timkostka/cert3d/firmware/GSL/inc/gsl_tim_defines.h

#pragma once

#include "gsl_includes.h"

// pins structure
struct GSL_TIM_PinsStruct {
  // CH1
  PinEnum ch1;
  // CH2
  PinEnum ch2;
  // CH3
  PinEnum ch3;
  // CH4
  PinEnum ch4;
  // ETR
  PinEnum etr;
  // CH1N
  PinEnum ch1n;
  // CH2N
  PinEnum ch2n;
  // CH3N
  PinEnum ch3n;
};

// timer trigger mapping
struct GSL_TIM_TriggerStruct {
  TIM_TypeDef * target;
  TIM_TypeDef * source;
  uint32_t trigger;
};

// hold trigger mappings between timers
const GSL_TIM_TriggerStruct gsl_tim_trigger[] = {
    {TIM1, TIM5, TIM_TS_ITR0},
    {TIM1, TIM2, TIM_TS_ITR1},
    {TIM1, TIM3, TIM_TS_ITR2},
    {TIM1, TIM4, TIM_TS_ITR3},

    {TIM8, TIM1, TIM_TS_ITR0},
    {TIM8, TIM2, TIM_TS_ITR1},
    {TIM8, TIM4, TIM_TS_ITR2},
    {TIM8, TIM5, TIM_TS_ITR3},

    {TIM2, TIM1, TIM_TS_ITR0},
    {TIM2, TIM8, TIM_TS_ITR1},
    {TIM2, TIM3, TIM_TS_ITR2},
    {TIM2, TIM4, TIM_TS_ITR3},

    {TIM3, TIM1, TIM_TS_ITR0},
    {TIM3, TIM2, TIM_TS_ITR1},
    {TIM3, TIM5, TIM_TS_ITR2},
    {TIM3, TIM4, TIM_TS_ITR3},

    {TIM4, TIM1, TIM_TS_ITR0},
    {TIM4, TIM2, TIM_TS_ITR1},
    {TIM4, TIM3, TIM_TS_ITR2},
    {TIM4, TIM8, TIM_TS_ITR3},

    {TIM5, TIM2, TIM_TS_ITR0},
    {TIM5, TIM3, TIM_TS_ITR1},
    {TIM5, TIM4, TIM_TS_ITR2},
    {TIM5, TIM8, TIM_TS_ITR3},

    {TIM9, TIM2, TIM_TS_ITR0},
    {TIM9, TIM3, TIM_TS_ITR1},

    {TIM12, TIM4, TIM_TS_ITR0},
    {TIM12, TIM5, TIM_TS_ITR1},
};

// number of triggers
const uint16_t gsl_tim_trigger_count =
    sizeof(gsl_tim_trigger) / sizeof(*gsl_tim_trigger);

// ************
// *** TIM1 ***
// ************

// TIM1_CH1 pin
#ifndef GSL_TIM1_PIN_CH1
#define GSL_TIM1_PIN_CH1 kPinA8
#endif

// TIM1_CH2 pin
#ifndef GSL_TIM1_PIN_CH2
#define GSL_TIM1_PIN_CH2 kPinA9
#endif

// TIM1_CH3 pin
#ifndef GSL_TIM1_PIN_CH3
#define GSL_TIM1_PIN_CH3 kPinA10
#endif

// TIM1_CH4 pin
#ifndef GSL_TIM1_PIN_CH4
#define GSL_TIM1_PIN_CH4 kPinA11
#endif

// TIM1_ETR pin
#ifndef GSL_TIM1_PIN_ETR
#define GSL_TIM1_PIN_ETR kPinA12
#endif

// TIM1_CH1N pin
#ifndef GSL_TIM1_PIN_CH1N
#define GSL_TIM1_PIN_CH1N kPinA7
#endif

// TIM1_CH2N pin
#ifndef GSL_TIM1_PIN_CH2N
#define GSL_TIM1_PIN_CH2N kPinB0
#endif

// TIM1_CH3N pin
#ifndef GSL_TIM1_PIN_CH3N
#define GSL_TIM1_PIN_CH3N kPinB1
#endif

// pins
GSL_TIM_PinsStruct gsl_tim1_pins = {
    GSL_TIM1_PIN_CH1,
    GSL_TIM1_PIN_CH2,
    GSL_TIM1_PIN_CH3,
    GSL_TIM1_PIN_CH4,
    GSL_TIM1_PIN_ETR,
    GSL_TIM1_PIN_CH1N,
    GSL_TIM1_PIN_CH2N,
    GSL_TIM1_PIN_CH3N};

// structure for handling TIM1 functions
TIM_HandleTypeDef gsl_tim1_htim = {
    TIM1,
    {
        0xFFFF, // Prescaler
        TIM_COUNTERMODE_UP, // CounterMode
        0xFFFF, // Period
        TIM_CLOCKDIVISION_DIV1, // ClockDivision
        0x00, // RepetitionCounter
    },
    HAL_TIM_ACTIVE_CHANNEL_CLEARED,
    {nullptr, nullptr, nullptr, nullptr, nullptr, nullptr, nullptr},
    HAL_UNLOCKED,
    HAL_TIM_STATE_RESET};

// ************
// *** TIM2 ***
// ************

// TIM2_CH1 pin
#ifndef GSL_TIM2_PIN_CH1
#define GSL_TIM2_PIN_CH1 kPinA0
#endif

// TIM2_CH2 pin
#ifndef GSL_TIM2_PIN_CH2
#define GSL_TIM2_PIN_CH2 kPinA1
#endif

// TIM2_CH3 pin
#ifndef GSL_TIM2_PIN_CH3
#define GSL_TIM2_PIN_CH3 kPinA2
#endif

// TIM2_CH4 pin
#ifndef GSL_TIM2_PIN_CH4
#define GSL_TIM2_PIN_CH4 kPinA3
#endif

// TIM2_ETR pin
#ifndef GSL_TIM2_PIN_ETR
#define GSL_TIM2_PIN_ETR kPinA5
#endif

// pins
GSL_TIM_PinsStruct gsl_tim2_pins = {
    GSL_TIM2_PIN_CH1,
    GSL_TIM2_PIN_CH2,
    GSL_TIM2_PIN_CH3,
    GSL_TIM2_PIN_CH4,
    GSL_TIM2_PIN_ETR,
    kPinInvalid,
    kPinInvalid,
    kPinInvalid};

// structure for handling TIM2 functions
TIM_HandleTypeDef gsl_tim2_htim = {
    TIM2,
    {
        0xFFFF, // Prescaler
        TIM_COUNTERMODE_UP, // CounterMode
        0xFFFF, // Period
        TIM_CLOCKDIVISION_DIV1, // ClockDivision
        0x00, // RepetitionCounter
    },
    HAL_TIM_ACTIVE_CHANNEL_CLEARED,
    {nullptr, nullptr, nullptr, nullptr, nullptr, nullptr, nullptr},
    HAL_UNLOCKED,
    HAL_TIM_STATE_RESET};

// ************
// *** TIM3 ***
// ************

// TIM3_CH1 pin
#ifndef GSL_TIM3_PIN_CH1
#define GSL_TIM3_PIN_CH1 kPinA6
#endif

// TIM3_CH2 pin
#ifndef GSL_TIM3_PIN_CH2
#define GSL_TIM3_PIN_CH2 kPinA7
#endif

// TIM3_CH3 pin
#ifndef GSL_TIM3_PIN_CH3
#define GSL_TIM3_PIN_CH3 kPinB0
#endif

// TIM3_CH4 pin
#ifndef GSL_TIM3_PIN_CH4
#define GSL_TIM3_PIN_CH4 kPinB1
#endif

// TIM3_ETR pin
#ifndef GSL_TIM3_PIN_ETR
#define GSL_TIM3_PIN_ETR kPinD2
#endif

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

#ifdef TIM7

// TIM7_CH1 pin
#define GSL_TIM7_PIN_CH1 kPinInvalid

// TIM7_CH2 pin
#define GSL_TIM7_PIN_CH2 kPinInvalid

// TIM7_CH3 pin
#define GSL_TIM7_PIN_CH3 kPinInvalid

// TIM7_CH4 pin
#define GSL_TIM7_PIN_CH4 kPinInvalid

// TIM7_ETR pin
#define GSL_TIM7_PIN_ETR kPinInvalid

// pins
GSL_TIM_PinsStruct gsl_tim7_pins = {
    GSL_TIM7_PIN_CH1,
    GSL_TIM7_PIN_CH2,
    GSL_TIM7_PIN_CH3,
    GSL_TIM7_PIN_CH4,
    GSL_TIM7_PIN_ETR,
    kPinInvalid,
    kPinInvalid,
    kPinInvalid};

// structure for handling TIM7 functions
TIM_HandleTypeDef gsl_tim7_htim = {
    TIM7,
    {
        0xFFFF, // Prescaler
        TIM_COUNTERMODE_UP, // CounterMode
        0xFFFF, // Period
        TIM_CLOCKDIVISION_DIV1, // ClockDivision
        0x00, // RepetitionCounter
    },
    HAL_TIM_ACTIVE_CHANNEL_CLEARED,
    {nullptr, nullptr, nullptr, nullptr, nullptr, nullptr, nullptr},
    HAL_UNLOCKED,
    HAL_TIM_STATE_RESET};

#endif

// ************
// *** TIM8 ***
// ************

#ifdef TIM8

// TIM8_CH1 pin
#ifndef GSL_TIM8_PIN_CH1
#define GSL_TIM8_PIN_CH1 kPinC6
#endif

// TIM8_CH2 pin
#ifndef GSL_TIM8_PIN_CH2
#define GSL_TIM8_PIN_CH2 kPinC7
#endif

// TIM8_CH3 pin
#ifndef GSL_TIM8_PIN_CH3
#define GSL_TIM8_PIN_CH3 kPinC8
#endif

// TIM8_CH4 pin
#ifndef GSL_TIM8_PIN_CH4
#define GSL_TIM8_PIN_CH4 kPinC9
#endif

// TIM8_ETR pin
#ifndef GSL_TIM8_PIN_ETR
#define GSL_TIM8_PIN_ETR kPinA0
#endif

// TIM8_CH1N pin
#ifndef GSL_TIM8_PIN_CH1N
#define GSL_TIM8_PIN_CH1N kPinA5
#endif

// TIM8_CH2N pin
#ifndef GSL_TIM8_PIN_CH2N
#define GSL_TIM8_PIN_CH2N kPinB14
#endif

// TIM8_CH3N pin
#ifndef GSL_TIM8_PIN_CH3N
#define GSL_TIM8_PIN_CH3N kPinB15
#endif

// pins
GSL_TIM_PinsStruct gsl_tim8_pins = {
    GSL_TIM8_PIN_CH1,
    GSL_TIM8_PIN_CH2,
    GSL_TIM8_PIN_CH3,
    GSL_TIM8_PIN_CH4,
    GSL_TIM8_PIN_ETR,
    kPinInvalid,
    kPinInvalid,
    kPinInvalid};

// structure for handling TIM8 functions
TIM_HandleTypeDef gsl_tim8_htim = {
    TIM8,
    {
        0xFFFF, // Prescaler
        TIM_COUNTERMODE_UP, // CounterMode
        0xFFFF, // Period
        TIM_CLOCKDIVISION_DIV1, // ClockDivision
        0x00, // RepetitionCounter
    },
    HAL_TIM_ACTIVE_CHANNEL_CLEARED,
    {nullptr, nullptr, nullptr, nullptr, nullptr, nullptr, nullptr},
    HAL_UNLOCKED,
    HAL_TIM_STATE_RESET};

#endif

// ************
// *** TIM9 ***
// ************

#ifdef TIM9

// TIM9_CH1 pin
#ifndef GSL_TIM9_PIN_CH1
#define GSL_TIM9_PIN_CH1 kPinA2
#endif

// TIM9_CH2 pin
#ifndef GSL_TIM9_PIN_CH2
#define GSL_TIM9_PIN_CH2 kPinA3
#endif

// TIM9_CH3 pin
#define GSL_TIM9_PIN_CH3 kPinInvalid

// TIM9_CH4 pin
#define GSL_TIM9_PIN_CH4 kPinInvalid

// TIM9_ETR pin
#define GSL_TIM9_PIN_ETR kPinInvalid

// pins
GSL_TIM_PinsStruct gsl_tim9_pins = {
    GSL_TIM9_PIN_CH1,
    GSL_TIM9_PIN_CH2,
    GSL_TIM9_PIN_CH3,
    GSL_TIM9_PIN_CH4,
    GSL_TIM9_PIN_ETR,
    kPinInvalid,
    kPinInvalid,
    kPinInvalid};

// structure for handling TIM9 functions
TIM_HandleTypeDef gsl_tim9_htim = {
    TIM9,
    {
        0xFFFF, // Prescaler
        TIM_COUNTERMODE_UP, // CounterMode
        0xFFFF, // Period
        TIM_CLOCKDIVISION_DIV1, // ClockDivision
        0x00, // RepetitionCounter
    },
    HAL_TIM_ACTIVE_CHANNEL_CLEARED,
    {nullptr, nullptr, nullptr, nullptr, nullptr, nullptr, nullptr},
    HAL_UNLOCKED,
    HAL_TIM_STATE_RESET};

#endif

// *************
// *** TIM10 ***
// *************

#ifdef TIM10

// TIM10_CH1 pin
#ifndef GSL_TIM10_PIN_CH1
#define GSL_TIM10_PIN_CH1 kPinB8
#endif

// TIM10_CH2 pin
#define GSL_TIM10_PIN_CH2 kPinInvalid

// TIM10_CH3 pin
#define GSL_TIM10_PIN_CH3 kPinInvalid

// TIM10_CH4 pin
#define GSL_TIM10_PIN_CH4 kPinInvalid

// TIM10_ETR pin
#define GSL_TIM10_PIN_ETR kPinInvalid

// pins
GSL_TIM_PinsStruct gsl_tim10_pins = {
    GSL_TIM10_PIN_CH1,
    GSL_TIM10_PIN_CH2,
    GSL_TIM10_PIN_CH3,
    GSL_TIM10_PIN_CH4,
    GSL_TIM10_PIN_ETR,
    kPinInvalid,
    kPinInvalid,
    kPinInvalid};

// structure for handling TIM10 functions
TIM_HandleTypeDef gsl_tim10_htim = {
    TIM10,
    {
        0xFFFF, // Prescaler
        TIM_COUNTERMODE_UP, // CounterMode
        0xFFFF, // Period
        TIM_CLOCKDIVISION_DIV1, // ClockDivision
        0x00, // RepetitionCounter
    },
    HAL_TIM_ACTIVE_CHANNEL_CLEARED,
    {nullptr, nullptr, nullptr, nullptr, nullptr, nullptr, nullptr},
    HAL_UNLOCKED,
    HAL_TIM_STATE_RESET};

#endif

// *************
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
        RCC_APB2ENR_TIM9EN,
    },
#endif // #ifdef TIM9

#ifdef TIM10
    {
        TIM10,
        &gsl_tim10_htim,
        &gsl_tim10_pins,
        TIM1_UP_TIM10_IRQn,
        nullptr,
        false,
        &RCC->APB2ENR,
        RCC_APB2ENR_TIM10EN,
    },
#endif // #ifdef TIM10

#ifdef TIM11
    {
        TIM11,
        &gsl_tim11_htim,
        &gsl_tim11_pins,
        TIM1_TRG_COM_TIM11_IRQn,
        nullptr,
        false,
        &RCC->APB2ENR,
        RCC_APB2ENR_TIM11EN,
    },
#endif // #ifdef TIM11

#ifdef TIM12
    {
        TIM12,
        &gsl_tim12_htim,
        &gsl_tim12_pins,
        TIM8_BRK_TIM12_IRQn,
        nullptr,
        false,
        &RCC->APB1ENR,
        RCC_APB1ENR_TIM12EN,
    },
#endif // #ifdef TIM12

#ifdef TIM13
    {
        TIM13,
        &gsl_tim13_htim,
        &gsl_tim13_pins,
        TIM8_UP_TIM13_IRQn,
        nullptr,
        false,
        &RCC->APB1ENR,
        RCC_APB1ENR_TIM13EN,
    },
#endif // #ifdef TIM3

#ifdef TIM14
    {
        TIM14,
        &gsl_tim14_htim,
        &gsl_tim14_pins,
        TIM8_TRG_COM_TIM14_IRQn,
        nullptr,
        false,
        &RCC->APB1ENR,
        RCC_APB1ENR_TIM14EN,
    },
#endif // #ifdef TIM14

};

// number of TIM peripherals
const uint32_t GSL_TIM_PeripheralCount =
    sizeof(GSL_TIM_Info) / sizeof(*GSL_TIM_Info);

// bytes of RAM used to store all the handler structs
const uint32_t GSL_TIM_StorageByteCount =
    sizeof(GSL_TIM_Info) +
    GSL_TIM_PeripheralCount * sizeof(TIM_HandleTypeDef) +
    GSL_TIM_PeripheralCount * sizeof(GSL_TIM_PinsStruct);

// timer to use for path processing callback
//TIM_TypeDef * const qb_process_timer = TIM2;
