timkostka/cert3d/ScopePanel.py

"""
This implements a custom wx control to view .

"""

import time
import math
import wx

from dpi import asize

from Data import *

# maximum edges per screen
max_points_per_screen = 1000

# screen size in pixels
screen_size = 1000

# possible colors for signals
all_signal_colors = [
    ("Red", wx.RED),
    ("Orange", wx.Colour(255, 127, 0)),
    ("Yellow", wx.YELLOW),
    ("Green", wx.GREEN),
    ("Cyan", wx.CYAN),
    ("Blue", wx.BLUE),
    ("Magenta", wx.Colour(255, 0, 255)),
    ("White", wx.WHITE),
]


class Signal:
    """A Signal holds information about a scope signal."""

    def __init__(self, name=None, color=wx.GREEN, thickness=1, data=None):
        # raw data
        assert isinstance(data, Data)
        # name of the signal
        self.name = name
        # color of channel
        self.color = color
        # width of the channel plot in pixels
        self.thickness = thickness
        # active data set
        self.active_data = data
        # start time of the data
        self.start_time = data.start_time
        # data cluster
        self.data_cluster = [[0, data]]

    def create_simplified_data_sets(self):
        """Create simplified data sets."""
        # create simplified data sets
        if len(self.data_cluster) > 1:
            del self.data_cluster[1:]
        data = self.get_master_data()
        while data.get_point_count() > max_points_per_screen:
            new_data = data.get_reduced_data()
            if new_data is None:
                break
            self.data_cluster.append([0, new_data])
            data = new_data
        # find zoom levels for each set
        for i in range(len(self.data_cluster)):
            data = self.data_cluster[i][1]
            min_seconds = data.get_min_period_with_point_count(
                max_points_per_screen
            )
            min_pixels_per_second = screen_size / min_seconds
            self.data_cluster[i][0] = min_pixels_per_second
        # DEBUG
        if False:
            print([(x[1].get_point_count(), x[0]) for x in self.data_cluster])
        # set min zoom level of most simplified set to 0
        self.data_cluster[-1][0] = 0.0

    def get_master_data(self):
        return self.data_cluster[0][1]

    def is_empty(self):
        """Return True if the signal is empty."""
        return bool(self.data_cluster)

    def set_active_data(self, pixels_per_second):
        """Set the active data based on the pixels_per_second value."""
        raise NotImplementedError

    def get_start_time(self):
        """Return the start time of the signal data in seconds."""
        if not self.active_data or self.active_data.is_empty():
            return 0.0
        return self.active_data.get_time_at_index(0)

    def get_length(self):
        """Return the length of the signal data in seconds."""
        if not self.active_data:
            return 0.0
        return self.active_data.get_length()

    def draw_signal(self, *args, **kwargs):
        """Draw the signal"""
        if not self.active_data:
            return
        self.active_data.draw_signal(*args, **kwargs)


class ScopeChannel:
    def __init__(self, height=30, low_value=0.0, high_value=1.0, signal=None):
        # height of channel in pixels
        self.height = height
        # value at low end of channel
        # (not used for bilevel or tristate signals)
        self.low_value = None
        # value at high end of channel
        # (not used for bilevel or tristate signals)
        self.high_value = None
        # signals within this scope channel
        self.signals = []
        # add data if needed
        if signal:
            self.add_signal(signal)

    def add_signal(self, signal):
        self.signals.append(signal)

    def draw(self, dc):
        """Draw the channel clipped to the given rectangle DC."""
        raise NotImplementedError


class ScopePanel(wx.ScrolledWindow):
    """A ScopePanel is a custom wxWidget to display oscilloscope-type data."""

    def __init__(self, parent, id_, position, size, style):
        super().__init__(parent, id_, position, size, style)
        # get estimated number of pixels per screen
        global screen_size
        screen_size = asize(1920)
        # create popup menu for signal style
        self.style_popup_menu = self.create_style_menu()
        self.SetBackgroundStyle(wx.BG_STYLE_PAINT)
        # list of channels
        self.channels = []
        # maximum zoom level to 10 pixels per ns
        self.maximum_pixels_per_second = asize(5) / 1e-9
        # minimum zoom level
        self.minimum_pixels_per_second = 0.0
        # index of selected channel, or None
        self.selected_channel_index = None
        # link to vertical scroll bar
        self.vertical_scroll_bar = None
        # (channel_index, y_value) used during rearranging channels
        self.dragging_channel = None
        # width of the snaptime display
        self.snaptime_frame_thickness = asize(1)
        # color of snaptime display
        self.snaptime_frame_color = wx.YELLOW
        # color of snaptime text
        self.snaptime_text_color = wx.WHITE
        # padding between name and channel data
        self.padding2 = asize(2)
        # thickness in pixels of channel separator bar
        self.channel_separator_thickness = 1
        # padding between channels
        self.padding = 2 * asize(2) + self.channel_separator_thickness
        # margin in pixels all around
        self.margin = asize(2)
        # spacing between signals
        self.signal_spacing = asize(2)
        # padding around timestamp label
        self.padding_timestamp_label = asize(1)
        # length of channel
        self.channel_length = asize(120)
        # leftmost time
        self.start_time = 0.0
        # zoom factor in pixels per second
        self.pixels_per_second = 1.0
        # mouse panning memory
        self.panning = False
        self.panning_start = 0
        # holds the (channel_index, signal_index) for a style menu popup
        self.signal_to_style = None
        # true when we're selecting a time delta
        self.selecting_time = False
        # maximum distance in pixels to snap to a time value
        self.snap_distance = asize(10)
        # offset in y pixels
        self.y_offset = 0
        # desired height to fit all channels in pixels
        self.desired_height = 0
        # minimum time of all data
        self.minimum_time = 0.0
        # maximum time of all data
        self.maximum_time = 0.0
        # delta time unit for horizontal axis (e.g. 10e-9)
        self.best_dt = None
        # highlighted point
        # (time, y_pixel)
        self.highlighted_point = None
        # name of the dt (e.g. "10 ns")
        self.best_dt_text = None
        # font for signal lables
        self.font_signal_name = wx.Font(
            9,
            wx.FONTFAMILY_MODERN,
            wx.FONTSTYLE_NORMAL,
            wx.FONTWEIGHT_BOLD,
            False,
            "Consolas",
        )
        # get height of signal names in pixels
        dc = wx.ClientDC(self)
        dc.SetFont(self.font_signal_name)
        # height of a signal name in pixels
        self.signal_name_height = dc.GetFullTextExtent("X")[1]
        # print("Signal name height is", self.signal_name_height)
        # font for timestamps
        self.font_timestamp = wx.Font(
            9,
            wx.FONTFAMILY_MODERN,
            wx.FONTSTYLE_NORMAL,
            wx.FONTWEIGHT_BOLD,
            False,
            "Calibri",
        )
        # margin for snaptime label
        self.snaptime_margin = [1, 0]
        # either None or (channel_index, signal_index, time)
        self.snaptime_start = None
        self.snaptime_end = None
        # prevent panel from shrinking too much
        self.SetMinSize((200, 200))
        # store stipple brushes
        self.stipple_brushes = {}
        # set background
        self.SetBackgroundColour(wx.BLACK)
        self.SetForegroundColour(wx.WHITE)

        self.Bind(wx.EVT_MENU, self.event_popup_menu_item_selected)
        self.Bind(wx.EVT_CONTEXT_MENU, self.event_show_popup)
        self.Bind(wx.EVT_PAINT, self.event_paint)
        self.Bind(wx.EVT_LEFT_DOWN, self.event_mouse_left_button_down)
        self.Bind(wx.EVT_LEFT_UP, self.event_mouse_left_button_up)
        self.Bind(wx.EVT_MIDDLE_DOWN, self.event_mouse_middle_button_down)
        self.Bind(wx.EVT_MIDDLE_UP, self.event_mouse_middle_button_up)
        self.Bind(wx.EVT_MOTION, self.event_mouse_motion)
        self.Bind(wx.EVT_LEAVE_WINDOW, self.event_leave_window)
        self.Bind(wx.EVT_MOUSEWHEEL, self.event_mouse_wheel)
        self.Bind(wx.EVT_SIZE, self.event_on_size)

        self.adjust_channel_name_size()

        # DEBUG populate sample data
        self.populate_example_data()

        self.zoom_to_all()

    def redo_scroll_bars(self):
        """Show/hide scroll bars based on current state."""
        self.SetScrollbars(1, 1, 1, self.desired_height)
        return
        # if no data, hide scroll bars
        width, height = self.GetSize()
        if not self.channels:
            show_vertical_bar = False
            show_horizontal_bar = False
        else:
            # get y position of last channel
            show_vertical_bar = height < self.desired_height
        # see if we need to show or hide the vertical bar
        vertical_bar_shown = self.GetParent().scroll_bar_vertical.IsShown()
        # show or hide bar
        if vertical_bar_shown != show_vertical_bar:
            self.GetParent().scroll_bar_vertical.Show(show_vertical_bar)
        # if vertical bar is hidden, we have no offset
        if not show_vertical_bar:
            self.y_offset = 0
        # update ticks
        if show_vertical_bar:
            self.GetParent().scroll_bar_vertical.SetScrollbar(
                self.y_offset, height, self.desired_height, asize(10)
            )
        return
        horizontal_bar_shown = self.GetParent().show_horizontal_bar.IsShown()
        # find x pixel of leftmost time
        x_low = self.get_x_from_time(self.minimum_time)
        x_high = self.get_x_from_time(self.maximum_time)
        # get first x pixel
        first_x = self.margin + self.channel_length + self.padding2
        # TODO: implement this
        show_horizontal_bar = x_low < first_x

        # either show or hide horizontal bar
        if horizontal_bar_shown != show_horizontal_bar:
            self.GetParent().scroll_bar_horizontal.Show(show_horizontal_bar)
        # update horizontal bar
        wanted_width = 0

    def event_on_size(self, _event):
        self.redo_scroll_bars()

    def clear(self):
        """Erase all channels."""
        self.channels = []

    def populate_example_data(self):
        """Populate the display with fabricated."""
        self.clear()
        # add some junk data
        for name in [
            "X_STEP",
            "X_DIR",
            "Y_STEP",
            "Y_DIR",
            "Z_STEP",
            "Z_DIR",
            "E_STEP",
            "E_DIR",
        ]:
            # create a random signal
            if "DIR" in name and False:
                data = TriStateData()
            else:
                data = BilevelData()
            data.invent_data(2000)
            signal = Signal(name=name, color=wx.GREEN, thickness=1, data=data)
            signal.create_simplified_data_sets()
            # create a channel for this signal
            channel = ScopeChannel(height=40, signal=signal)
            # add this channel
            self.add_channel(channel)
        for i in range(3):
            name = 'FuzzyData%d' % i
            data = FuzzyPlotData()
            signal = Signal(name=name, color=wx.GREEN, thickness=1, data=data)
            channel = ScopeChannel(height=120, signal=signal)
            self.add_channel(channel)
        for name in ["X_POS", "Y_POS", "Z_POS", "E_POS"]:
            data = PlotData()
            data.invent_data(5000)
            signal = Signal(name=name, color=wx.CYAN, thickness=1, data=data)
            signal.create_simplified_data_sets()
            channel = ScopeChannel(height=120, signal=signal)
            self.add_channel(channel)

    def adjust_channel_name_size(self):
        """Find ideal value for self.channel_length."""
        max_length = 0
        dc = wx.ClientDC(self)
        dc.SetFont(self.font_signal_name)
        for channel in self.channels:
            for signal in channel.signals:
                rect = dc.GetFullTextExtent(signal.name)
                max_length = max(max_length, rect[0])
        if max_length > 0:
            self.channel_length = max_length + asize(5)

    def create_style_menu(self):
        """Create and return a wx.Menu for the signal style popup."""
        menu = wx.Menu()
        # add colors
        # item = menu.Append(-1, "Color")
        submenu = wx.Menu()
        for (name, color) in all_signal_colors:
            submenu.AppendRadioItem(-1, name)
        menu.AppendSubMenu(submenu, "&Color")
        # add thickness submenu
        submenu = wx.Menu()
        for i in range(1, 6):
            submenu.AppendRadioItem(-1, str(i))
        menu.AppendSubMenu(submenu, "&Thickness")
        menu.Append(wx.MenuItem(menu, -1, "&Master data"))
        menu.Append(wx.MenuItem(menu, -1, "&All master data"))
        return menu

    def update_desired_height(self):
        if not self.channels:
            self.desired_height = 0
            return
        # update desired height
        self.desired_height = 2 * self.margin
        self.desired_height += (len(self.channels) - 1) * self.padding
        self.desired_height += sum(x.height for x in self.channels)

    def add_channel(self, channel):
        """Add a new channel."""
        self.channels.append(channel)
        self.update_desired_height()

    def get_channel_from_y(self, y):
        """Return the channel index for the given y pixel, or None."""
        for i in range(len(self.channels)):
            y1, y2 = self.get_channel_y_values(i)
            # return None if we've passed it already
            if y1 > y:
                return None
            if y1 <= y <= y2:
                return i
        # return None if we're past the end of the data
        return None

    def get_signal_from_y(self, y):
        """Return the channel and signal index from the y pixel, or None."""
        channel_index = self.get_channel_from_y(y)
        if channel_index is None:
            return None
        # search through signals in this channel
        signal_count = len(self.channels[channel_index].signals)
        y1, y2 = self.get_channel_y_values(channel_index)
        # get y value of middle of channel
        y_mid = (y1 + y2) // 2
        # get y value of first signal
        name_height = (
            signal_count * self.signal_name_height
            + (signal_count - 1) * self.signal_spacing
        )
        y_top = y_mid - name_height // 2
        for signal_index in range(signal_count):
            if signal_index > 0:
                y_top += self.signal_spacing + self.signal_name_height
            if y_top <= y < y_top + self.signal_name_height:
                return channel_index, signal_index
        # return None if we're past the end of the data
        return None

    def find_snaptime(self, position):
        """Return the snaptime at the given position, or None"""
        # find correct channel
        x, y = position
        channel_index = self.get_channel_from_y(y)
        if channel_index is None:
            return None
        # alias this channel
        channel = self.channels[channel_index]
        # convert pixel position to a time
        target_time = self.get_time_from_x(x)
        # hold a list of closest time for each signal within the channel
        best_delta = 0.0
        closest_time = None
        # find the closest x value for each signal within the channel
        for signal_index, signal in enumerate(channel.signals):
            this_time = signal.active_data.get_edge_near_time(target_time)
            if this_time is not None:
                this_delta = abs(this_time - target_time)
                if closest_time is None or this_delta < best_delta:
                    best_delta = this_delta
                    closest_time = (channel_index, signal_index, this_time)
        if closest_time is None:
            return None
        # find delta in pixels
        pixel_delta = int(best_delta * self.pixels_per_second + 0.5)
        if abs(pixel_delta) < self.snap_distance:
            return closest_time
        return None

    def event_mouse_left_button_down(self, event):
        # we either try to drag a channel, or try to select a snapline
        x_separator = self.margin + self.channel_length + self.padding2
        if event.GetPosition()[0] < x_separator:
            # reset snaptime if present
            y = event.GetPosition()[1]
            for i in range(len(self.channels)):
                y1, y2 = self.get_channel_y_values(i)
                if y1 <= y <= y2:
                    # print('Dragging channel', self.dragging_channel)
                    self.dragging_channel = (i, y - y1)
                    self.selected_channel_index = i
                    self.Refresh()
                    break
        else:
            # find closest
            old_start = self.snaptime_start
            old_end = self.snaptime_end
            self.snaptime_start = None
            self.snaptime_end = None
            self.snaptime_start = self.find_snaptime(event.GetPosition())
            if (
                self.snaptime_start != old_start
                or self.snaptime_end != old_end
            ):
                self.Refresh()
            self.selecting_time = bool(self.snaptime_start)

    def event_mouse_left_button_up(self, event):
        if self.dragging_channel:
            self.dragging_channel = None
            self.selected_channel_index = None
            self.Refresh()
        self.selecting_time = False
        if self.snaptime_start:
            self.snaptime_end = self.find_snaptime(event.GetPosition())
            if (
                not self.snaptime_end
                or self.snaptime_end == self.snaptime_start
            ):
                self.snaptime_start = None
                self.snaptime_end = None
            self.Refresh()

    def get_time_at_mouse(self, event):
        """Return the time at the mouse coordinates."""
        pass

    def event_leave_window(self, event):
        if self.panning:
            self.event_mouse_middle_button_up(event)
        if self.dragging_channel:
            self.event_mouse_left_button_up(event)

    def event_mouse_middle_button_down(self, event):
        # print('right button down')
        x = event.GetPosition()[0]
        if x >= self.margin + self.channel_length + self.padding2:
            self.panning_start = x
            self.panning = True
            self.SetCursor(wx.Cursor(wx.CURSOR_SIZEWE))

    def event_mouse_middle_button_up(self, _event):
        # print('right button up')
        if self.panning:
            self.SetCursor(wx.Cursor(wx.CURSOR_DEFAULT))
            self.panning = False

    def event_mouse_motion(self, event):
        if self.panning:
            dx = event.GetPosition()[0] - self.panning_start
            # if no net motion, just return
            if not dx:
                return
            # print('moved by %d pixels' % dx)
            delta = dx / self.pixels_per_second
            self.start_time -= delta
            self.panning_start += dx
            self.Refresh()
        elif self.dragging_channel:
            # get offset into current channel as-is
            index, offset = self.dragging_channel
            y1, _ = self.get_channel_y_values(index)
            this_offset = event.GetPosition()[1] - y1
            # get target amount of pixels to move channel
            current_delta = this_offset - offset
            chan = self.channels
            if current_delta > 0 and index < len(self.channels) - 1:
                # set a 2 pixel hysteresis
                current_delta -= 1
                # get delta if we move channel down
                increase = self.channels[index + 1].height + self.padding
                # see if it's advantageous to move it
                if abs(current_delta - increase) < abs(current_delta):
                    chan[index], chan[index + 1] = chan[index + 1], chan[index]
                    index += 1
                    self.dragging_channel = (index, offset)
                    self.selected_channel_index = index
                    self.Refresh()
            elif current_delta < 0 and index > 0:
                # set a 2 pixel hysteresis
                current_delta += 1
                # get delta if we move channel up
                increase = self.channels[index - 1].height + self.padding
                # see if it's advantageous to move it
                if abs(current_delta + increase) < abs(current_delta):
                    chan[index - 1], chan[index] = chan[index], chan[index - 1]
                    index -= 1
                    self.dragging_channel = (index, offset)
                    self.selected_channel_index = index
                    self.Refresh()
        elif self.snaptime_start and self.selecting_time:
            new_end = self.find_snaptime(event.GetPosition())
            if new_end != self.snaptime_end:
                self.snaptime_end = new_end
                if self.snaptime_end == self.snaptime_start:
                    self.snaptime_end = None
                self.Refresh()
        else:
            y = event.GetPosition()[1]
            channel_index = None
            for i in range(len(self.channels)):
                y1, y2 = self.get_channel_y_values(i)
                if y1 <= y <= y2:
                    # print('Dragging channel', self.dragging_channel)
                    channel_index = i
                    break
            if channel_index is None:
                return
            # find tick value
            signal = self.channels[channel_index].signals[0]
            x = event.GetPosition()[0]
            x_separator = self.margin + self.channel_length + self.padding2
            if x < x_separator:
                return
            x -= x_separator
            t = self.start_time + x / self.pixels_per_second
            i = signal.active_data.find_closest_index(t)
            if i is None:
                return
            text = "index %d, time %g" % (channel_index, t)
            if isinstance(signal.active_data, PlotData):
                y = signal.active_data.points[i][1]
                text += ", value=%g" % y
            self.GetParent().GetParent().GetParent().status_bar.SetStatusText(text)

    def event_mouse_wheel(self, event):
        """Handle scrolling in/out via the mouse wheel."""
        scale = 2.0 ** (1.0 / 3.0)
        # if Ctrl is held, zoom faster
        if wx.GetKeyState(wx.WXK_SHIFT):
            scale = 2.0
        if event.GetWheelRotation() < 0:
            scale = 1.0 / scale
        dx = self.margin + self.channel_length + self.padding2
        # get min and max scale
        max_scale = self.maximum_pixels_per_second / self.pixels_per_second
        min_scale = self.minimum_pixels_per_second / self.pixels_per_second
        assert min_scale <= max_scale
        # clip scale to min, max bounds
        scale = max(min_scale, min(scale, max_scale))
        # adjust start time so time at cursor remains the same
        x = event.GetPosition()[0]
        # apply the scale
        if scale != 1.0:
            self.pixels_per_second *= scale
            self.start_time -= (x - dx) / self.pixels_per_second * (1 - scale)
            self.update_signal_zoom()
            self.Refresh()

    def get_x_from_time(self, duration):
        """Return the x pixels corresponding to the given duration."""
        x = self.margin + self.channel_length + self.padding2
        x += (duration - self.start_time) * self.pixels_per_second
        return int(x + 0.5)

    def get_time_from_x(self, x):
        """Return the time value corresponding to the x position."""
        x -= self.margin + self.channel_length + self.padding2
        return self.start_time + x / self.pixels_per_second

    def get_channel_y_values(self, channel_index):
        """Return the top and bottom y pixels for the given channel."""
        top = self.margin - self.y_offset
        top += sum(x.height for x in self.channels[:channel_index])
        top += channel_index * self.padding
        return top, top + self.channels[channel_index].height - 1

    def update_signal_zoom(self):
        """Find the best data for the given zoom level."""
        for channel in self.channels:
            for signal in channel.signals:
                if signal.is_empty():
                    signal.active_data = None
                signal.active_data = None
                for zoom, data in signal.data_cluster:
                    if zoom < self.pixels_per_second:
                        signal.active_data = data
                        break
                assert signal.active_data is not None

    def zoom_to_all(self, include_zero=True):
        """Initialize the viewing window to see all data."""
        if not self.channels:
            return
        start_times = []
        end_times = []
        for channel in self.channels:
            for signal in channel.signals:
                start = signal.get_start_time()
                length = signal.get_length()
                start_times.append(start)
                end_times.append(start + length)
        left = min(start_times) if start_times else 0.0
        right = max(end_times) if end_times else 0.0
        panel_width = (
            self.GetSize()[0]
            - 2 * self.margin
            - self.padding2
            - self.channel_length
        )
        panel_width = max(panel_width, asize(200))
        self.start_time = left
        self.pixels_per_second = 1.0
        if right != left:
            self.pixels_per_second = (panel_width - 1) / (right - left)
        self.update_signal_zoom()
        self.Refresh()
        for channel in self.channels:
            low_values = []
            high_values = []
            for signal in channel.signals:
                data = signal.active_data
                if data.is_empty():
                    continue
                if isinstance(data, PlotData):
                    low_values.append(min(x[1] for x in data.points))
                    high_values.append(max(x[1] for x in data.points))
                elif isinstance(data, FuzzyPlotData):
                    low_values.append(min(x[1] for x in data.points))
                    high_values.append(max(x[2] for x in data.points))
            if low_values:
                channel.low_value = min(low_values)
                if include_zero:
                    channel.low_value = min(0.0, channel.low_value)
                channel.high_value = max(high_values)
                if include_zero:
                    channel.high_value = max(0.0, channel.high_value)
                if channel.low_value == channel.high_value:
                    channel.high_value = channel.low_value + 1e99

    def trim_signals(self, idle_ms=100):
        """Trim inactivity from the start and end of all signals."""
        # get first time of activity
        first_activity = []
        last_activity = []
        for channel in self.channels:
            for signal in channel.signals:
                data = signal.get_master_data()
                if isinstance(data, PlotData):
                    data.optimize()
                if data.get_point_count() < 2:
                    continue
                if isinstance(data, PlotData) or isinstance(data, FuzzyPlotData):
                    continue
                    if data.points[0][1] == data.points[1][1]:
                        first_activity.append(data.get_time_at_index(1))
                    else:
                        first_activity.append(data.get_time_at_index(0))
                    if data.points[-1][1] == data.points[-2][1]:
                        last_activity.append(data.get_time_at_index(-2))
                    else:
                        last_activity.append(data.get_time_at_index(-1))
                elif isinstance(data, BilevelData):
                    first_activity.append(data.get_time_at_index(1))
                    last_activity.append(data.get_time_at_index(-2))
                elif isinstance(data, TriStateData):
                    first_activity.append(data.get_time_at_index(1))
                    last_activity.append(data.get_time_at_index(-2))
                else:
                    raise ValueError("type %s is unexpected" % type(data))
        # find values to trim to
        if first_activity:
            start_time = min(first_activity) - idle_ms / 1000.0
        else:
            start_time = None
        if last_activity:
            end_time = max(last_activity) + idle_ms / 1000.0
        else:
            end_time = None
        if start_time > end_time:
            return
        # trim start
        if start_time:
            for channel in self.channels:
                for signal in channel.signals:
                    data = signal.get_master_data()
                    if (
                        data.is_empty()
                        or data.get_time_at_index(0) > start_time
                    ):
                        continue
                    tick = data.get_x_from_time(start_time)
                    if isinstance(data, BilevelData):
                        data.edges[0] = tick
                    else:
                        data.points[0] = (tick, data.points[0][1])
        if end_time:
            for channel in self.channels:
                for signal in channel.signals:
                    data = signal.get_master_data()
                    if (
                        data.is_empty()
                        or data.get_time_at_index(-1) < end_time
                    ):
                        continue
                    tick = data.get_x_from_time(end_time)
                    if isinstance(data, BilevelData):
                        data.edges[-1] = tick
                    else:
                        data.points[-1] = (tick, data.points[-1][1])
                    signal.create_simplified_data_sets()
        self.Refresh()

    @staticmethod
    def time_to_text(time_s):
        """Convert the time in seconds to a text value."""
        if time_s == 0:
            return "0"
        abstime = abs(time_s)
        if abstime < 10e-9:
            return "%.2f ns" % (time_s * 1e9)
        elif abstime < 100e-9:
            return "%.1f ns" % (time_s * 1e9)
        elif abstime < 1000e-9:
            return "%.0f ns" % (time_s * 1e9)
        elif abstime < 10e-6:
            return "%.2f us" % (time_s * 1e6)
        elif abstime < 100e-6:
            return "%.1f us" % (time_s * 1e6)
        elif abstime < 1000e-6:
            return "%.0f us" % (time_s * 1e6)
        elif abstime < 10e-3:
            return "%.2f ms" % (time_s * 1e3)
        elif abstime < 100e-3:
            return "%.1f ms" % (time_s * 1e3)
        elif abstime < 1000e-3:
            return "%.0f ms" % (time_s * 1e3)
        else:
            return "%g s" % time_s

    def find_dt(self):
        """Evaluate the best time delta for the given scale."""
        # get the width of some standard text
        dc = wx.PaintDC(self)
        dc.SetFont(
            wx.Font(
                9,
                wx.FONTFAMILY_MODERN,
                wx.FONTSTYLE_NORMAL,
                wx.FONTWEIGHT_NORMAL,
                False,
                "Consolas",
            )
        )
        rect = dc.GetFullTextExtent("Target width    ")
        target_width = rect[0]
        # print("Target dt width is %d pixels" % target_width)
        scale = [1.0, 1e-3, 1e-6, 1e-9]
        units = ["s", "ms", "us", "ns"]
        multiples = [1, 2, 5]
        target_dt = target_width / self.pixels_per_second
        # print("Looking for increment near %g s." % target_dt)
        # human dt
        best_diff = None
        best_dt = 0.0
        best_dt_text = None
        # best_dt_pixels = None
        for m in multiples:
            # find target of the form dt = m * 10^x for some interger x
            x = round(math.log10(target_dt / m))
            this_dt = m * 10 ** x
            this_diff = abs(target_dt - this_dt)
            if best_diff is None or this_diff < best_diff:
                best_diff = this_diff
                best_dt = this_dt
        # find the best text
        for unit, name in zip(scale, units):
            if unit <= best_dt:
                best_dt_text = "%d %s" % (round(best_dt / unit), name)
                break
        if best_dt_text is None and best_dt is not None:
            best_dt_text = "%g" % best_dt
        # print("Best dt was %s" % best_dt_text)
        self.best_dt = best_dt
        self.best_dt_text = best_dt_text

    def event_paint(self, _event):
        """Handle the EVT_PAINT event."""
        self.find_dt()
        dc = wx.AutoBufferedPaintDC(self)
        self.y_offset = self.GetViewStart()[1]
        # set drawing mode to overwrite
        dc.SetLogicalFunction(wx.COPY)
        # clear panel and fill with background color
        dc.Clear()
        # get leftmost pixel we can draw for scope view
        left = self.margin + self.channel_length + self.padding2
        # get size of panel
        panel_rect = self.GetSize()
        # get rightmost pixel to draw for scope view
        right = panel_rect[0] - 1
        # draw vertical bars for dt resolution
        dc.SetPen(wx.Pen(wx.Colour(31, 31, 31), 1))
        dt_pixels = round(self.best_dt * self.pixels_per_second)
        for x in range(left, right + 1, dt_pixels):
            dc.DrawRectangle(round(x), 0, 1, panel_rect[1])
        # get top pixel for next channel
        top = -self.y_offset
        timings = []
        # set font for channel name
        dc.SetFont(self.font_signal_name)
        for i, channel in enumerate(self.channels):
            timings.append(time.perf_counter())
            # if not the first channel, draw the separator
            if i == 0:
                top += self.margin
            else:
                thickness = self.channel_separator_thickness
                y0 = top + self.padding // 2 - thickness // 2
                dc.SetPen(wx.Pen(wx.Colour(31, 31, 31), 1))
                dc.SetBrush(wx.Brush(wx.Colour(31, 31, 31)))
                dc.DrawRectangle(0, y0, right + 1, thickness)
                top += self.padding
            # get top (y1) and bottom (y2) of display
            y1 = top
            y2 = y1 + channel.height - 1
            y_mid = (y1 + y2) // 2
            # highlight channel if it's selected
            if self.selected_channel_index == i:
                # draw background
                color = wx.Colour(63, 63, 63)
                dc.SetPen(wx.Pen(color, 1))
                dc.SetBrush(wx.Brush(color))
                add = self.padding // 2
                dc.DrawRectangle(0, y1 - add, right + 1, y2 - y1 + 1 + add * 2)
            # draw channel names
            signal_count = len(channel.signals)
            for signal_index, signal in enumerate(channel.signals):
                # set channel color
                dc.SetPen(wx.Pen(signal.color, 1))
                dc.SetBrush(wx.Brush(signal.color))
                dc.SetTextForeground(signal.color)
                name = signal.name
                # get x,y of middle center
                rect = dc.GetFullTextExtent(name)
                x = self.signal_spacing + self.channel_length
                # adjust for multiple signals per channel
                y = y_mid - rect[1] // 2
                y -= (signal_count - 1) * ((rect[1] + 5) // 2)
                y += signal_index * (rect[1] + 5)
                dc.DrawText(name, x - rect[0], y)
                # get rect to clip channel data to
                rect = wx.Rect(left, y1, right - left + 1, y2 - y1 + 1)
                # draw signal within this rect
                signal.draw_signal(
                    dc,
                    rect,
                    signal.color,
                    signal.thickness,
                    self.start_time,
                    self.pixels_per_second,
                    channel.low_value,
                    channel.high_value,
                )
            top += channel.height
        timings.append(time.perf_counter())
        # output timing information
        if False:
            print(
                "Timings: %s"
                % "/".join(
                    "%.3g" % (1000 * x)
                    for x in [
                        (timings[i + 1] - timings[i])
                        for i in range(len(self.channels))
                    ]
                )
            )
        # draw snap time
        if self.snaptime_start:
            # set clipping region to right half
            dc.SetClippingRegion(left, 0, panel_rect[0] - left, panel_rect[1])
            # get amount to offset due to snaptime frame thickness
            thickness = self.snaptime_frame_thickness
            delta = thickness // 2
            dc.SetPen(wx.Pen(self.snaptime_frame_color, 1))
            dc.SetBrush(wx.Brush(self.snaptime_frame_color))
            dc.SetTextForeground(self.snaptime_text_color)
            dc.SetTextBackground(wx.BLACK)
            dc.SetBackgroundMode(wx.SOLID)
            channel_index, _, start_time = self.snaptime_start
            x1 = self.get_x_from_time(start_time)
            y11, y12 = self.get_channel_y_values(channel_index)
            height = y12 - y11 + 1
            y11 += height // 6
            y12 -= height // 6
            y1 = (y11 + y12) / 2
            # draw start time selection
            dc.DrawRectangle(x1 - delta, y11, thickness, y12 - y11 + 1)
            if self.snaptime_end:
                channel_index, _, end_time = self.snaptime_end
                x2 = self.get_x_from_time(end_time)
                y21, y22 = self.get_channel_y_values(channel_index)
                height = y22 - y21 + 1
                y21 += height // 6
                y22 -= height // 6
                y2 = (y21 + y22) / 2
                # draw end time selection
                # dc.DrawLine(x2, y21, x2, y22)
                dc.DrawRectangle(x2 - delta, y21, thickness, y22 - y21 + 1)
                # draw line connecting them
                x3 = (x1 + x2) // 2
                # dc.DrawLine(x1, y1, x3, y1)
                dc.DrawRectangle(
                    x1 - delta, y1 - delta, x3 - x1 + thickness, thickness
                )
                # dc.DrawLine(x3, y1, x3, y2)
                dc.DrawRectangle(
                    x3 - delta, y1 - delta, thickness, y2 - y1 + thickness
                )
                # dc.DrawLine(x3, y2, x2, y2)
                dc.DrawRectangle(
                    x3 - delta, y2 - delta, x2 - x3 + thickness, thickness
                )
                # draw time between
                dc.SetFont(self.font_timestamp)
                text = self.time_to_text(end_time - start_time)
                rect = dc.GetFullTextExtent(text)
                width = rect[0]
                height = rect[1]
                # add space for padding between label and frame
                width += 2 * self.snaptime_margin[0]
                height += 2 * self.snaptime_margin[1]
                # add space for frame
                width += 2 * thickness
                height += 2 * thickness
                x = x3
                y = (y1 + y2) / 2
                x -= width // 2
                y -= height // 2
                dc.DrawRectangle(x, y, width, height)

                # draw background of text
                dc.SetBrush(wx.BLACK_BRUSH)
                dc.DrawRectangle(x, y, width, height)
                dc.SetBrush(wx.Brush(self.snaptime_frame_color))
                # draw text
                x += self.snaptime_margin[0] + thickness
                y += self.snaptime_margin[1] + thickness
                dc.DrawText(text, x, y)
                x -= self.snaptime_margin[0] + thickness
                y -= self.snaptime_margin[1] + thickness
                # draw a rectangle using lines
                dc.DrawRectangle(x, y, width, thickness)
                dc.DrawRectangle(x, y + height - thickness, width, thickness)
                dc.DrawRectangle(x, y, thickness, height)
                dc.DrawRectangle(x + width - thickness, y, thickness, height)

    def event_show_popup(self, event):
        x, y = self.ScreenToClient(event.GetPosition())
        # if we're in a signal name, show the popup for signal styles
        if x < self.margin + self.channel_length:
            result = self.get_signal_from_y(y)
            if result:
                self.signal_to_style = result
                channel_index, signal_index = result
                signal = self.channels[channel_index].signals[signal_index]
                # select correct radio box for thickness
                id_ = self.style_popup_menu.FindItem(str(signal.thickness))
                self.style_popup_menu.FindItemById(id_).Check()
                # select correct radio box for color
                color_name = next(
                    x for x, y in all_signal_colors if y == signal.color
                )
                id_ = self.style_popup_menu.FindItem(color_name)
                self.style_popup_menu.FindItemById(id_).Check()
                # popup the style submenu
                self.PopupMenu(self.style_popup_menu, (x, y))
        # only show
        # popup style menu if we're within a signal name

    def event_popup_menu_item_selected(self, event):
        # alias the signal to modify
        channel_index, signal_index = self.signal_to_style
        signal = self.channels[channel_index].signals[signal_index]
        # get the text of the menu item selected
        item = self.style_popup_menu.FindItemById(event.GetId())
        text = item.GetText()
        # if it's numeric, change the thickness, else change the color
        if text.isdigit():
            signal.thickness = int(text)
        elif text == '&Master data':
            signal.active_data = signal.get_master_data()
        elif text == '&All master data':
            for channel in self.channels:
                for this_signal in channel.signals:
                    this_signal.active_data = this_signal.get_master_data()
        else:
            color = next(y for x, y in all_signal_colors if x == text)
            signal.color = color
        # redraw the screen
        self.Refresh()
